BluGeni/Hextraction/STLs/Tiles/King/King Spring.stl

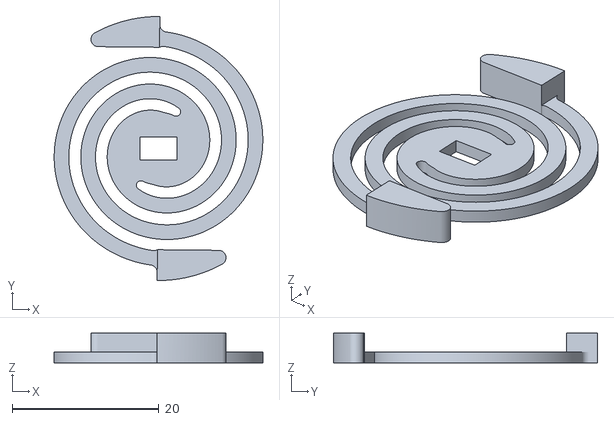
[picture p18: CAD file, 2023-05-18]
STLs/Tiles/King/King Spring.stl
28.5 x 36.0 x 4.05
