BluGeni/Hextraction/STLs/Tiles/Launcher/Launcher Tile Card.stl

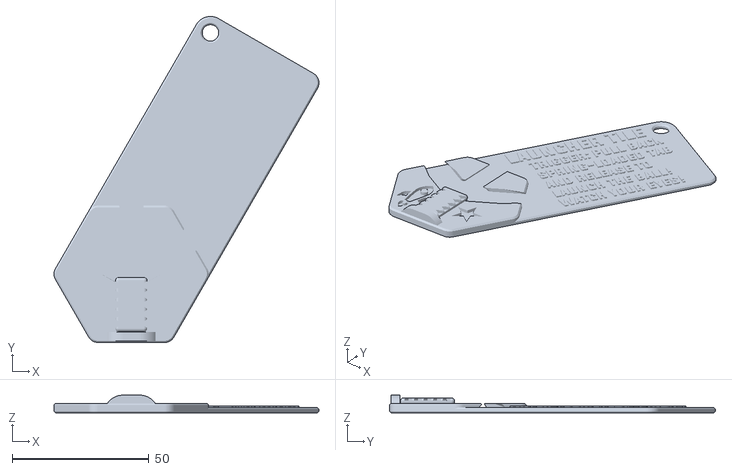
[picture p19: CAD file, 2023-05-18]
STLs/Tiles/Launcher/Launcher Tile Card.stl
96.8 x 119.1 x 6.50
