BluGeni/Hextraction/STLs/Tiles/Logo/Brand Tile 3A.stl

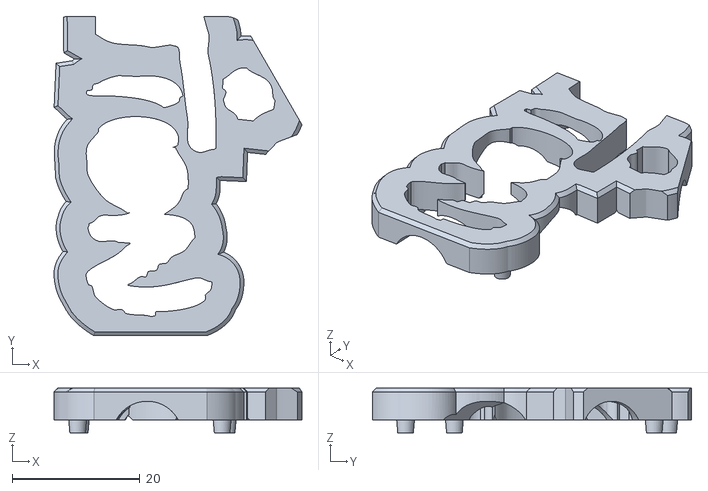
[picture p20: CAD file, 2023-05-18]
STLs/Tiles/Logo/Brand Tile 3A.stl
38.8 x 50.0 x 7.00
