BluGeni/Hextraction/STLs/Tiles/Nothing/Tile with Nothing.stl

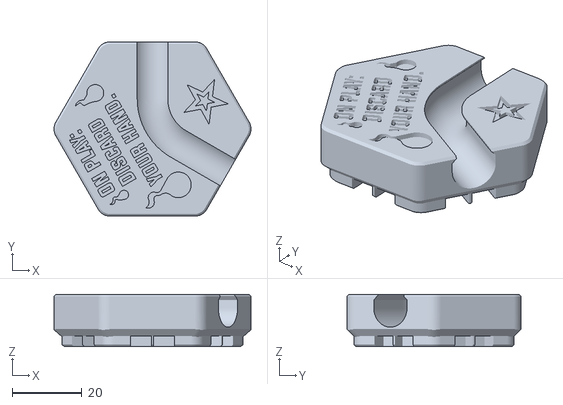
[picture p21: CAD file, 2023-05-18]
STLs/Tiles/Nothing/Tile with Nothing.stl
56.5 x 50.0 x 15.0
