BluGeni/Hextraction/STLs/Tiles/Pachinko/Pachinko Tile.stl

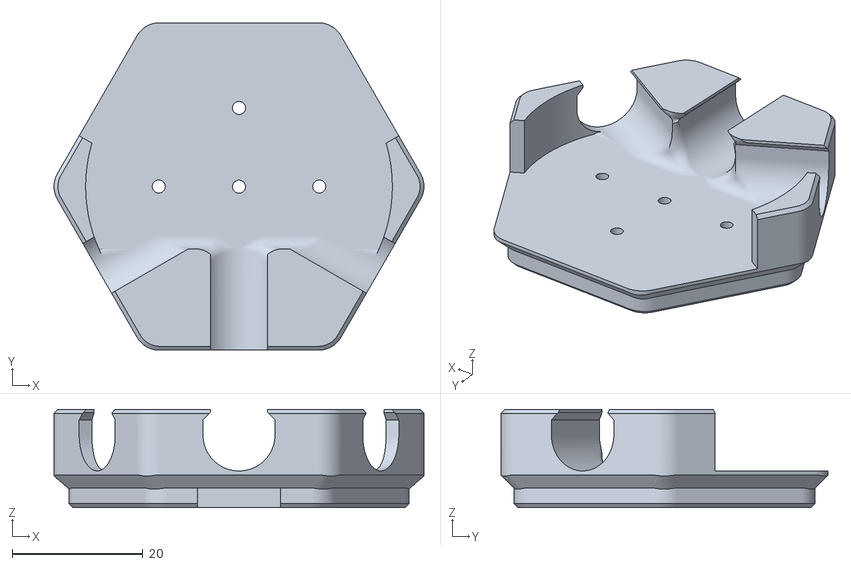
[picture p22: CAD file, 2023-05-18]
STLs/Tiles/Pachinko/Pachinko Tile.stl
56.5 x 50.0 x 15.0
