BluGeni/Hextraction/STLs/Tiles/SecretMystery/Secret Lid.stl

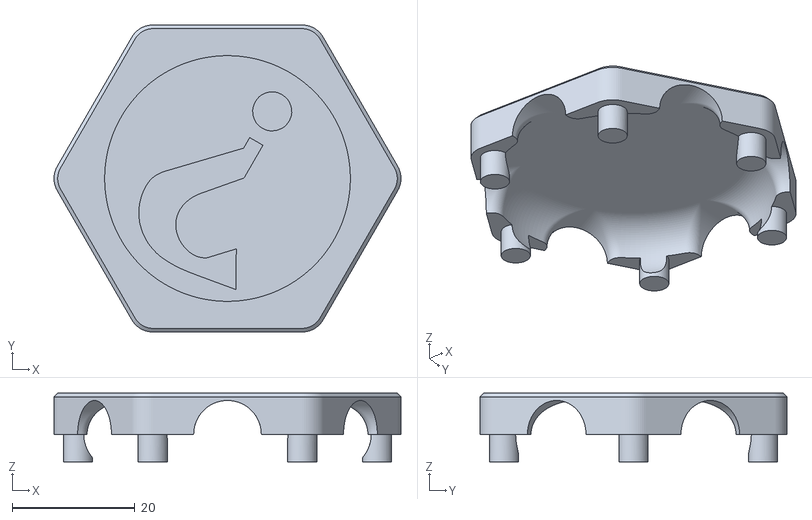
[picture p23: CAD file, 2023-05-18]
STLs/Tiles/SecretMystery/Secret Lid.stl
56.5 x 50.0 x 11.2
