BluGeni/Hextraction/STLs/Tiles/Seek/Seek Tile Multi Center.stl

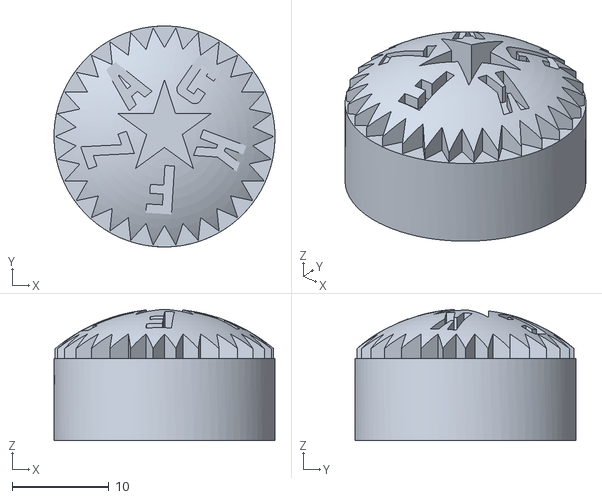
[picture p24: CAD file, 2023-05-18]
STLs/Tiles/Seek/Seek Tile Multi Center.stl
22.8 x 22.8 x 13.6
