BluGeni/Hextraction/STLs/Tiles/Sozu/Sozu Tile v27.stl

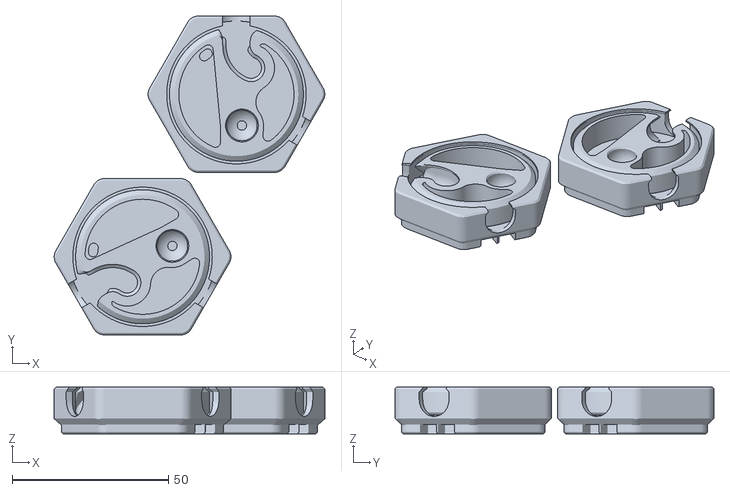
[picture p25: CAD file, 2023-05-18]
STLs/Tiles/Sozu/Sozu Tile v27.stl
86.5 x 102.0 x 15.0
