BluGeni/Hextraction/STLs/Tiles/Teleport/Teleport In Tile.stl

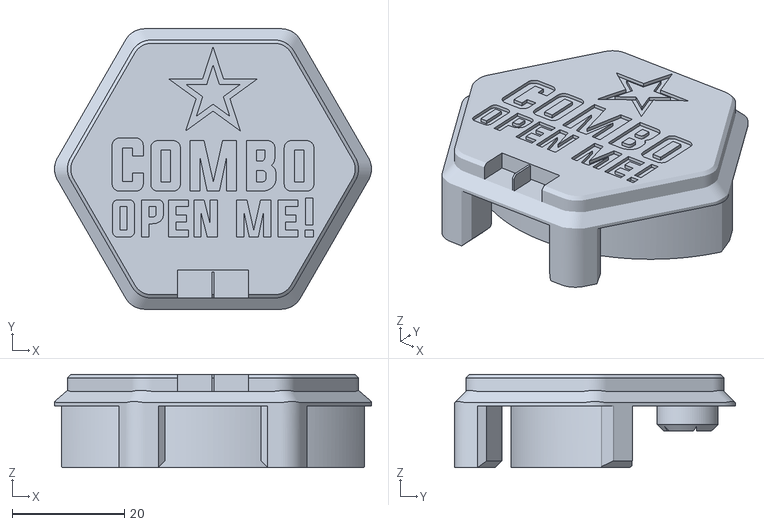
[picture p26: CAD file, 2023-05-18]
STLs/Tiles/Teleport/Teleport In Tile.stl
56.5 x 50.0 x 16.6
