BluGeni/Hextraction/STLs/Tiles/Zoidberg/Zoidberg Tile.stl

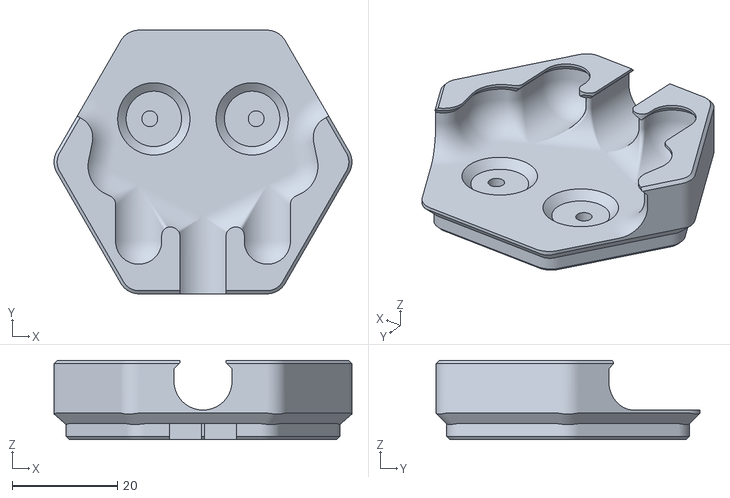
[picture p27: CAD file, 2023-05-18]
STLs/Tiles/Zoidberg/Zoidberg Tile.stl
56.5 x 50.0 x 15.0
