BluGeni/Hextraction/STLs/Tiles/aTemplate/Blank Tile.stl

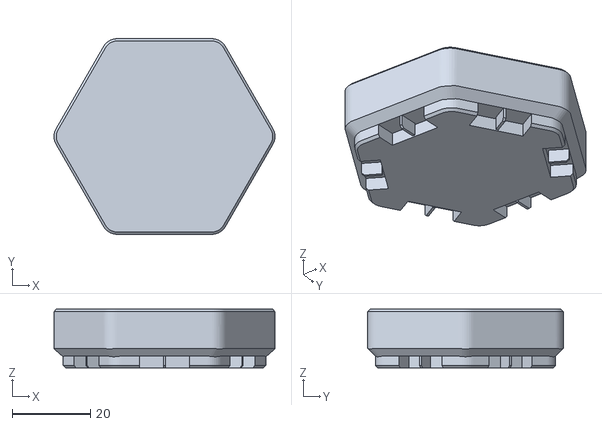
[picture p28: CAD file, 2023-05-18]
STLs/Tiles/aTemplate/Blank Tile.stl
56.5 x 50.0 x 15.0
