BluGeni/Hextraction/STLs/Tiles/Basic/DC Tile.stl

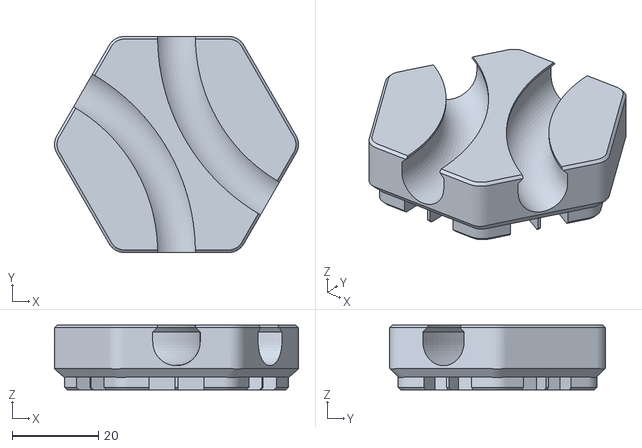
[picture p29: CAD file, 2023-05-18]
STLs/Tiles/Basic/DC Tile.stl
56.5 x 50.0 x 15.0
