BluGeni/Hextraction/STLs/Tiles/Built for Two/Double Tile Link.stl

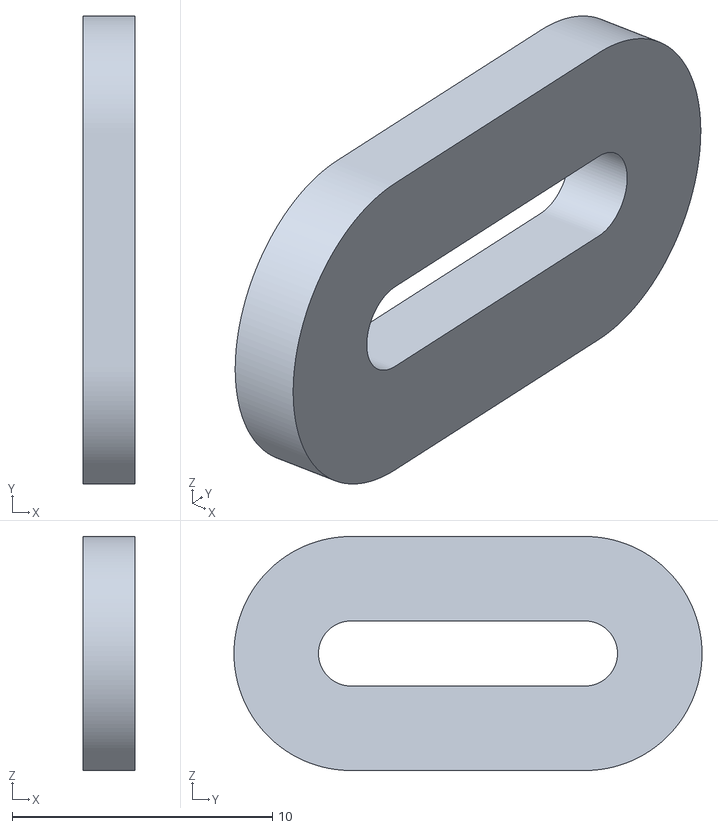
[picture p30: CAD file, 2023-05-18]
STLs/Tiles/Built for Two/Double Tile Link.stl
2.00 x 18.0 x 9.00
