BluGeni/Hextraction/STLs/Tiles/Cartoon Bomb/Bomb Tile Card.stl

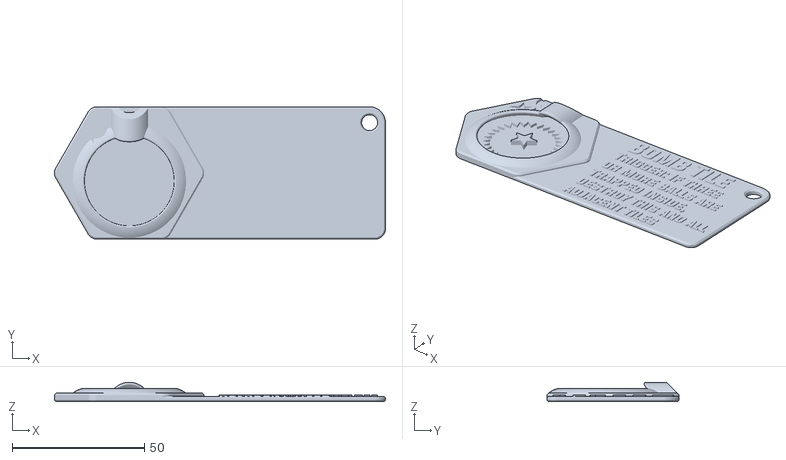
[picture p31: CAD file, 2023-05-18]
STLs/Tiles/Cartoon Bomb/Bomb Tile Card.stl
125.0 x 50.0 x 7.30
