BluGeni/Hextraction/STLs/Tiles/Double and Triple Trap/Triple Trap Tile.stl

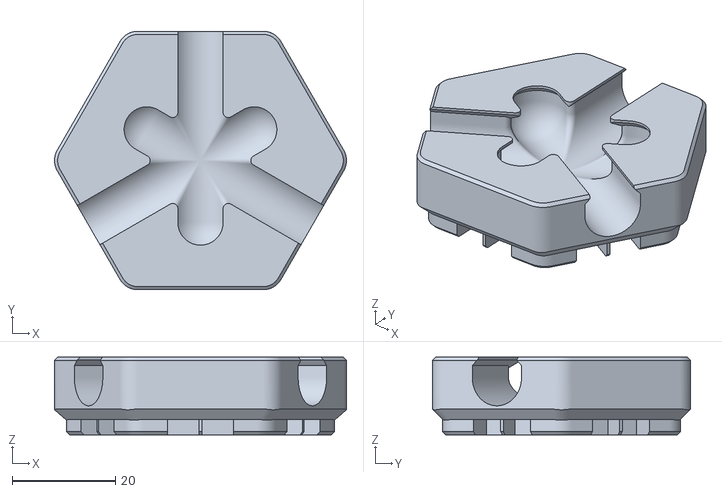
[picture p32: CAD file, 2023-05-18]
STLs/Tiles/Double and Triple Trap/Triple Trap Tile.stl
56.5 x 50.0 x 15.0
