BluGeni/Hextraction/STLs/Tiles/Flip-Flop/Flip Tile.step

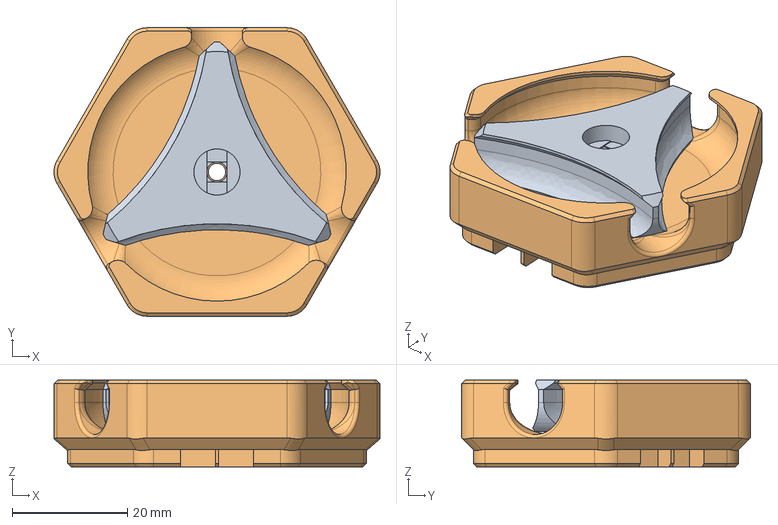
[picture p33: CAD file, 2023-05-18]
STLs/Tiles/Flip-Flop/Flip Tile.step
56.5 x 50.0 x 15.0 mm
Flippy Dingus
Tile (1)
