BluGeni/Hextraction/STLs/Tiles/Holographic/Holographic Hypertile v16.step

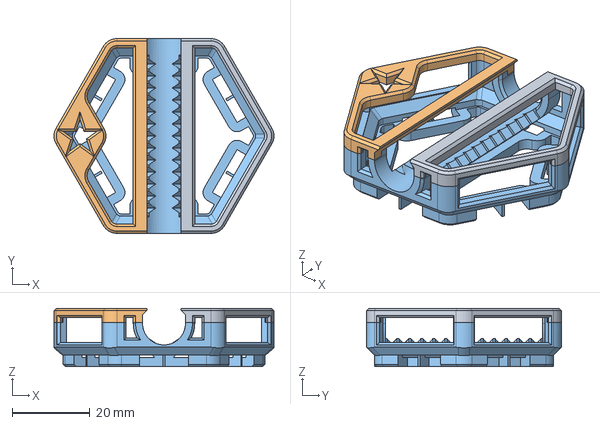
[picture p34: CAD file, 2023-05-18]
STLs/Tiles/Holographic/Holographic Hypertile v16.step
56.5 x 50.0 x 15.0 mm
