BluGeni/Hextraction/STLs/Tiles/King/King Upper.stl

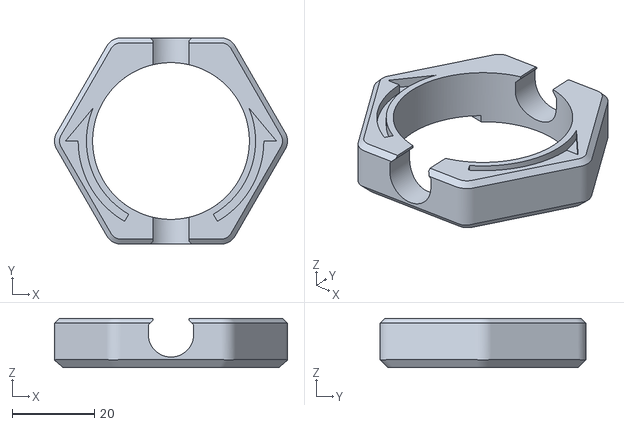
[picture p35: CAD file, 2023-05-18]
STLs/Tiles/King/King Upper.stl
56.5 x 50.0 x 12.0
