BluGeni/Hextraction/STLs/Tiles/Launcher/Launcher Tile.stl

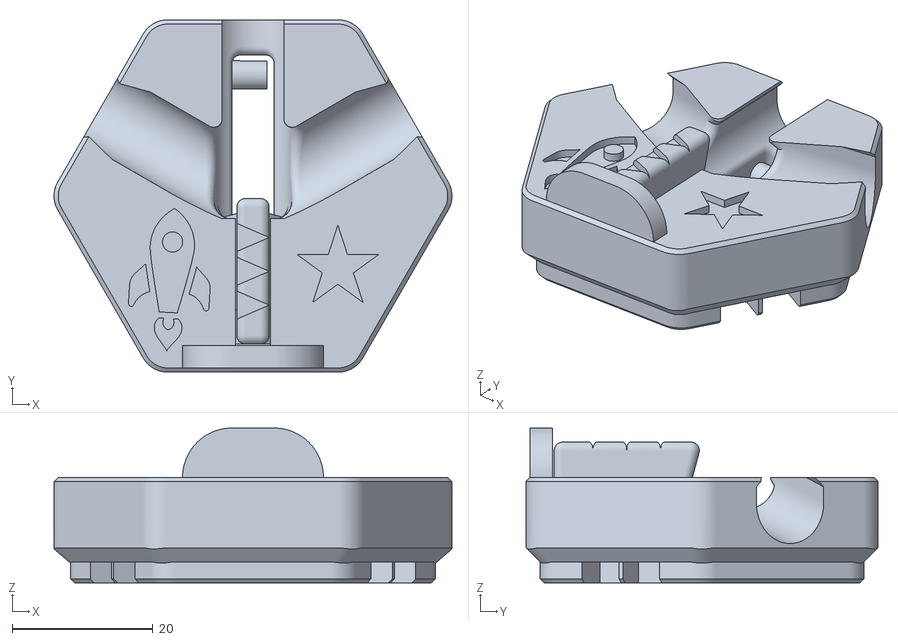
[picture p36: CAD file, 2023-05-18]
STLs/Tiles/Launcher/Launcher Tile.stl
56.5 x 50.0 x 22.0
