BluGeni/Hextraction/STLs/Tiles/Logo/Brand Tile 3B.stl

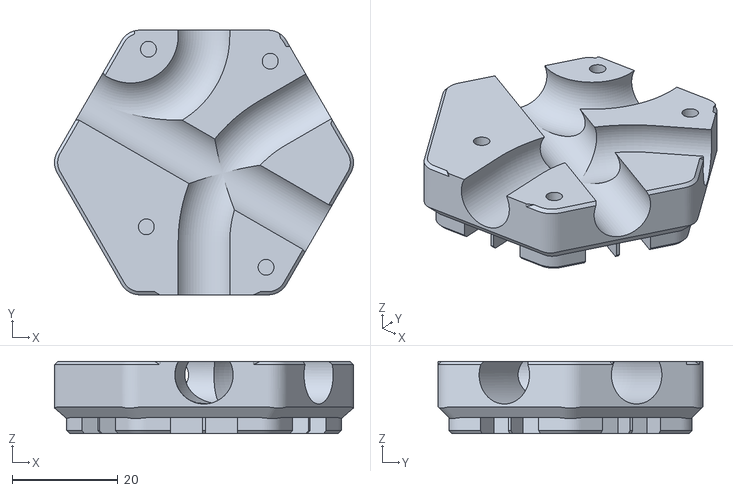
[picture p37: CAD file, 2023-05-18]
STLs/Tiles/Logo/Brand Tile 3B.stl
56.5 x 50.0 x 13.7
