BluGeni/Hextraction/STLs/Tiles/SecretMystery/Secret DC Body.stl

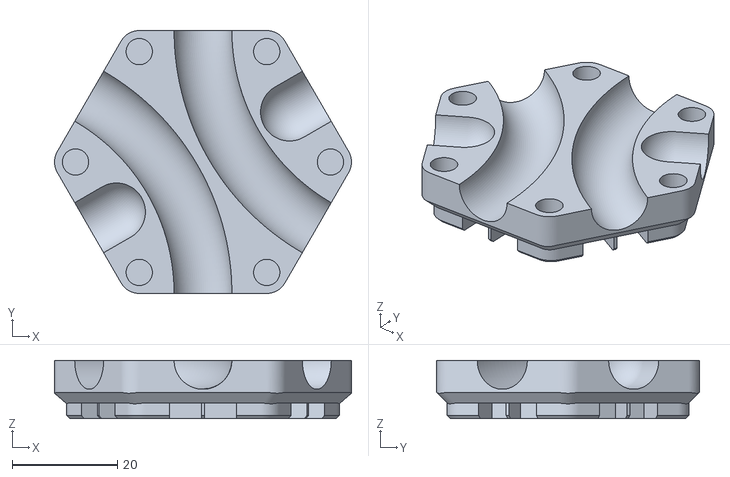
[picture p38: CAD file, 2023-05-18]
STLs/Tiles/SecretMystery/Secret DC Body.stl
56.5 x 50.0 x 11.1
