BluGeni/Hextraction/STLs/Tiles/Seek/Seek Tile Card.stl

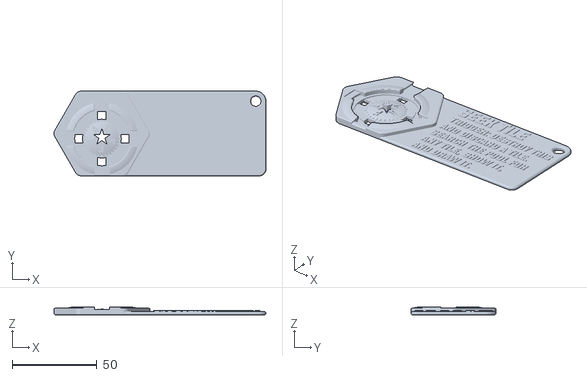
[picture p39: CAD file, 2023-05-18]
STLs/Tiles/Seek/Seek Tile Card.stl
125.0 x 50.0 x 4.73
