BluGeni/Hextraction/STLs/Game Board/Basic On-Ramp.stl

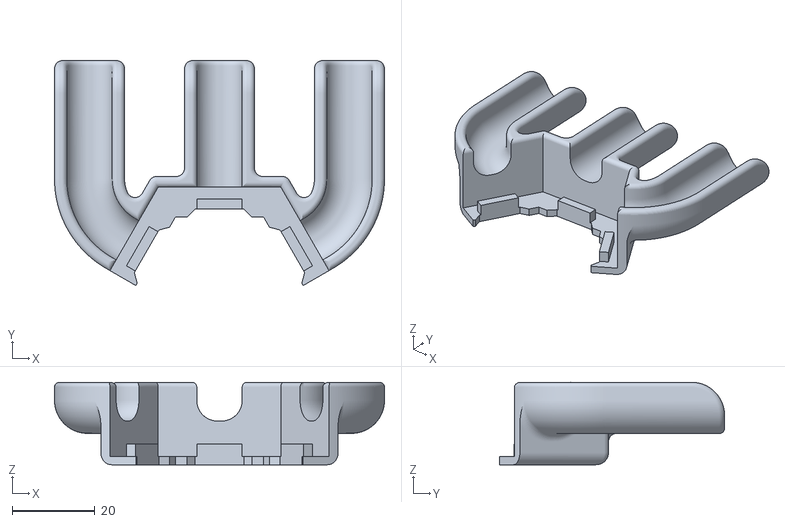
[picture p41: CAD file, 2023-05-18]
STLs/Game Board/Basic On-Ramp.stl
80.0 x 54.6 x 20.0
