BluGeni/Hextraction/STLs/Tiles/Basic/Peace Tile.stl

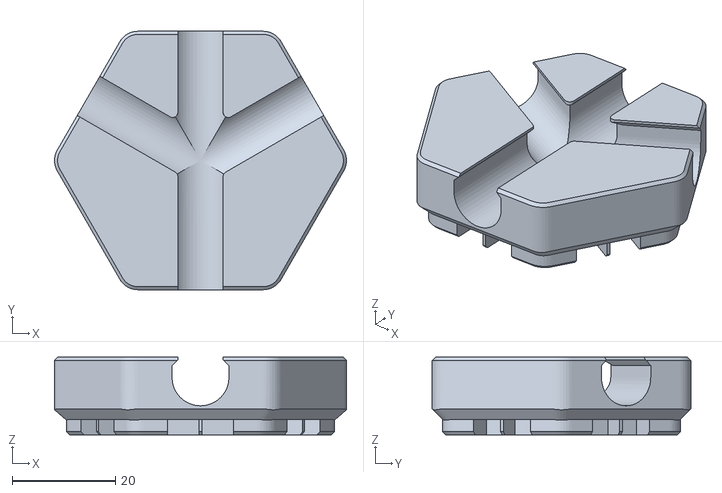
[picture p42: CAD file, 2023-05-18]
STLs/Tiles/Basic/Peace Tile.stl
56.5 x 50.0 x 15.0
