BluGeni/Hextraction/STLs/Tiles/Built for Two/Double Tile Top.stl

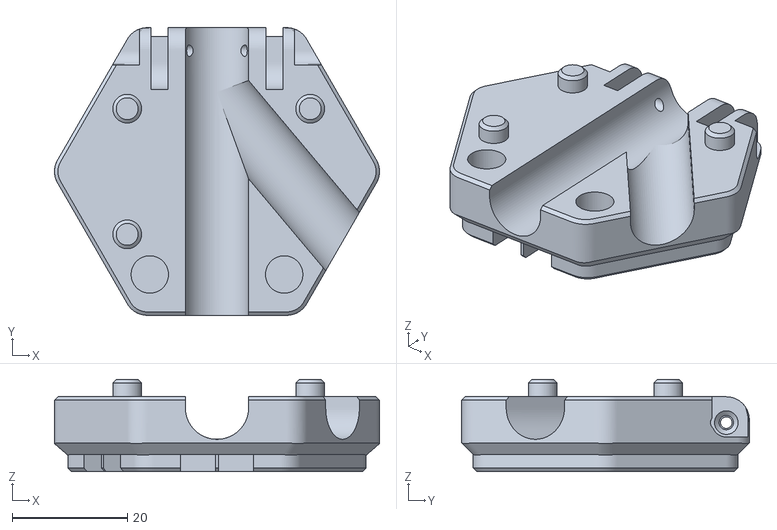
[picture p43: CAD file, 2023-05-18]
STLs/Tiles/Built for Two/Double Tile Top.stl
56.5 x 50.0 x 16.0
