BluGeni/Hextraction/STLs/Tiles/Flip-Flop/Flip Flop Tile Advanced.stl

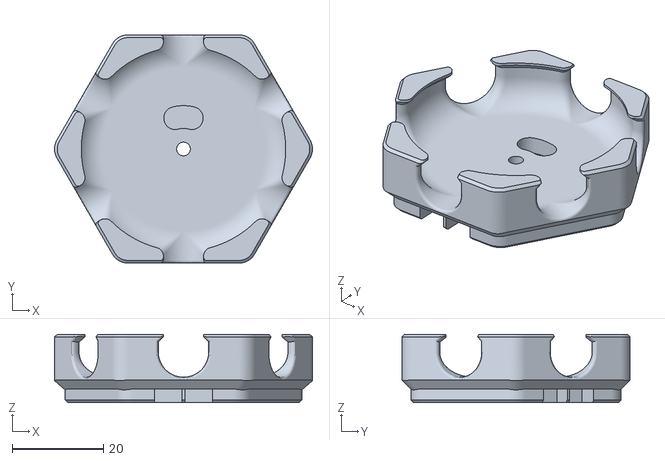
[picture p44: CAD file, 2023-05-18]
STLs/Tiles/Flip-Flop/Flip Flop Tile Advanced.stl
56.5 x 50.0 x 15.0
