BluGeni/Hextraction/STLs/Tiles/Holographic/Holo Bottom.stl

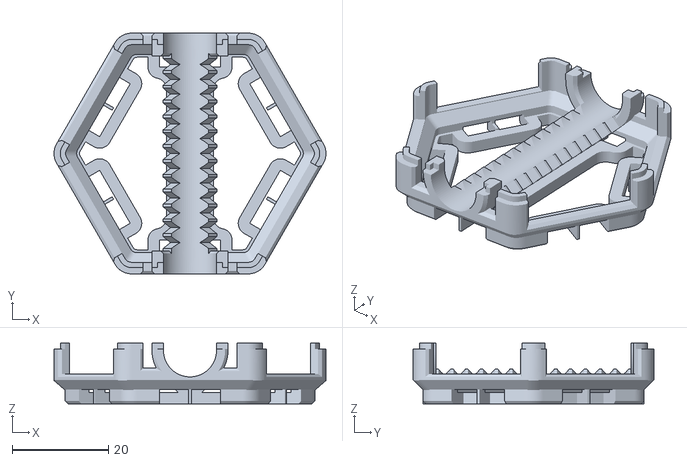
[picture p45: CAD file, 2023-05-18]
STLs/Tiles/Holographic/Holo Bottom.stl
56.5 x 50.0 x 12.6
