BluGeni/Hextraction/STLs/Tiles/King/King Lower.stl

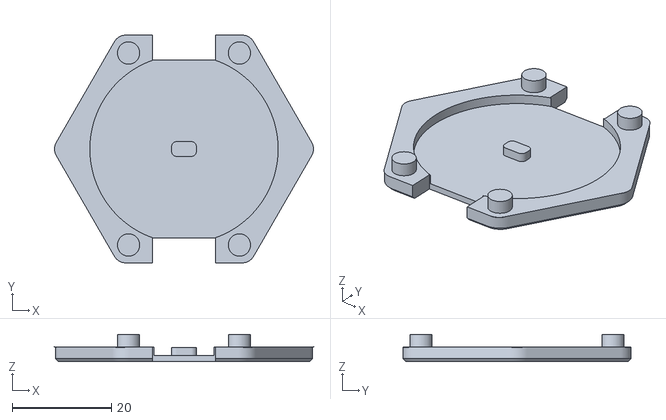
[picture p46: CAD file, 2023-05-18]
STLs/Tiles/King/King Lower.stl
52.3 x 46.0 x 5.50
