BluGeni/Hextraction/STLs/Tiles/Logo/Brand Tile 1A.stl

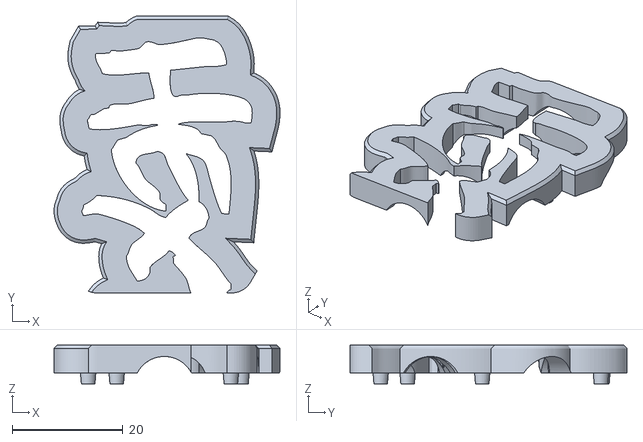
[picture p47: CAD file, 2023-05-18]
STLs/Tiles/Logo/Brand Tile 1A.stl
40.8 x 50.0 x 7.00
