BluGeni/Hextraction/STLs/Tiles/SecretMystery/Secret Inlay.stl

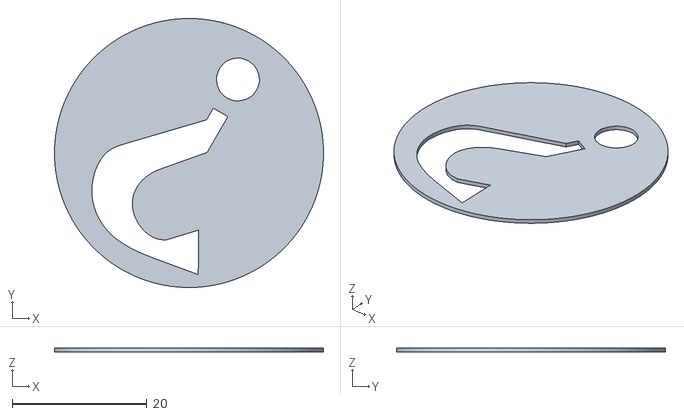
[picture p48: CAD file, 2023-05-18]
STLs/Tiles/SecretMystery/Secret Inlay.stl
40.0 x 40.0 x 0.6
