BluGeni/Hextraction/STLs/Tiles/Seek/Seek Tile One Piece.stl

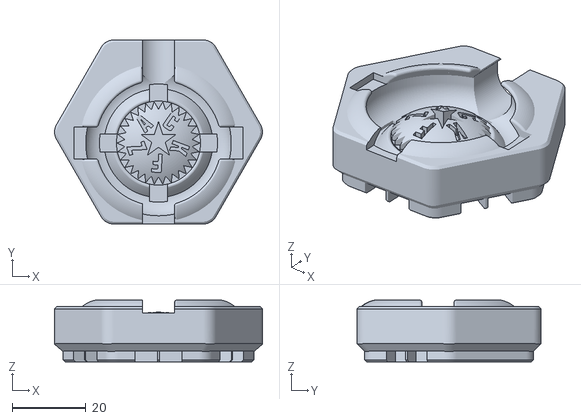
[picture p49: CAD file, 2023-05-18]
STLs/Tiles/Seek/Seek Tile One Piece.stl
56.5 x 50.0 x 16.8
