BluGeni/Hextraction/STLs/Tiles/Sozu/Sozu Flipper Right 3-8in.stl

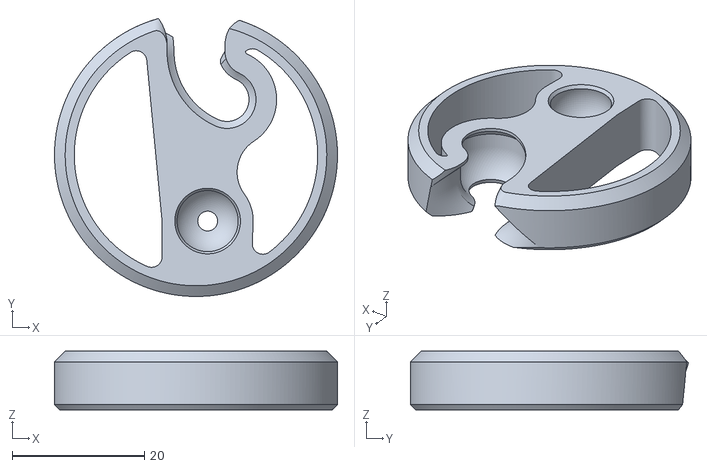
[picture p50: CAD file, 2023-05-18]
STLs/Tiles/Sozu/Sozu Flipper Right 3-8in.stl
42.8 x 42.0 x 8.90
