BluGeni/Hextraction/STLs/Tiles/Built for Two/Tile Built for Two v11.step

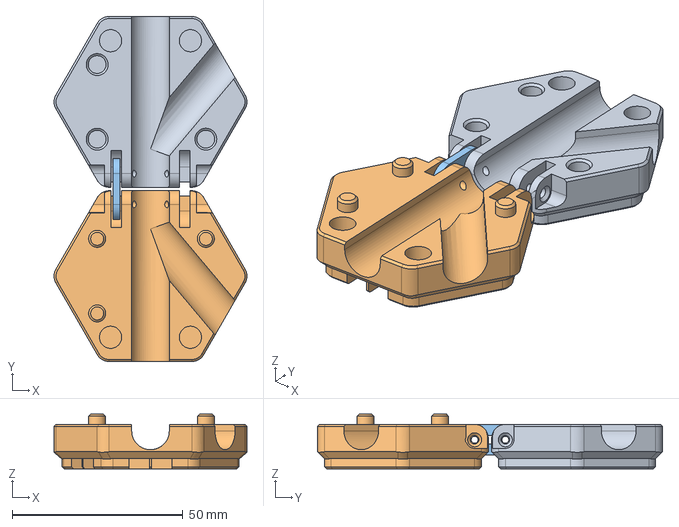
[picture p52: CAD file, 2023-05-18]
STLs/Tiles/Built for Two/Tile Built for Two v11.step
56.5 x 101.0 x 16.0 mm
