BluGeni/Hextraction/STLs/Tiles/Holographic/Holo Card.stl

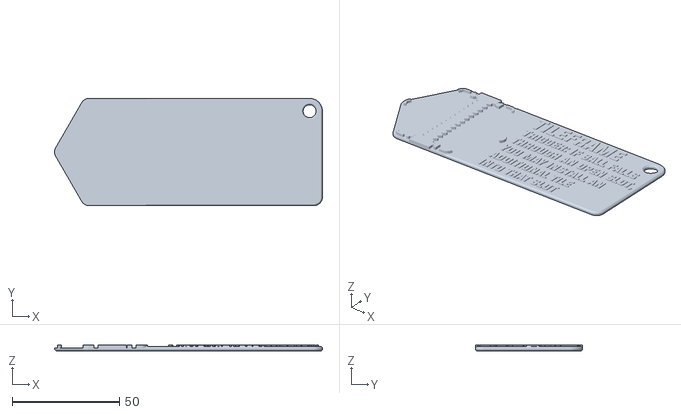
[picture p53: CAD file, 2023-05-18]
STLs/Tiles/Holographic/Holo Card.stl
125.0 x 50.0 x 2.60
