BluGeni/Hextraction/STLs/Tiles/King/King Tile v19.step

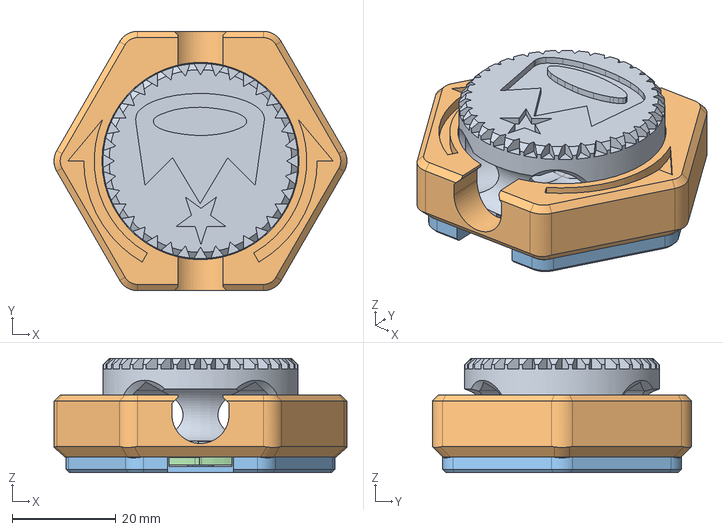
[picture p54: CAD file, 2023-05-18]
STLs/Tiles/King/King Tile v19.step
56.5 x 50.0 x 22.0 mm
