BluGeni/Hextraction/STLs/Tiles/Seek/Seek Tile Multi.stl

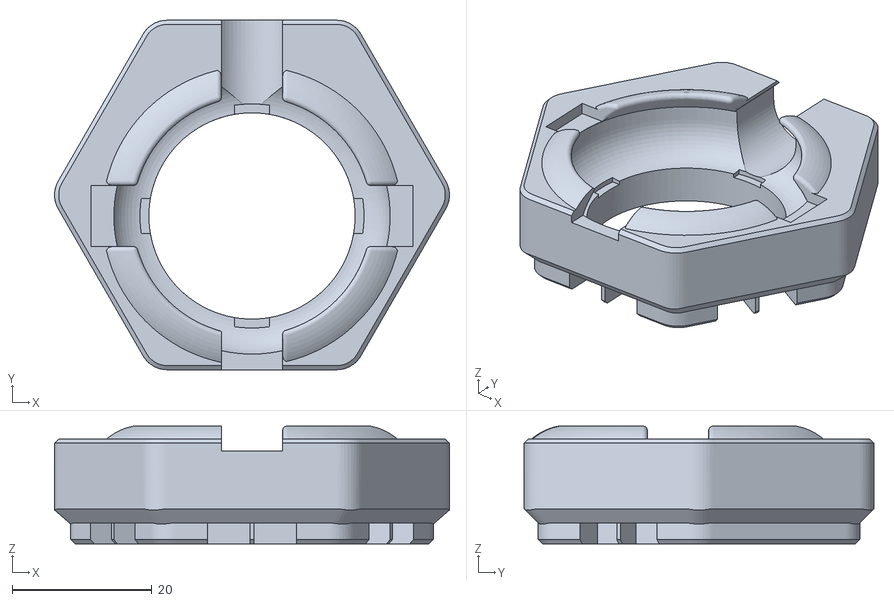
[picture p55: CAD file, 2023-05-18]
STLs/Tiles/Seek/Seek Tile Multi.stl
56.5 x 50.0 x 16.8
