BluGeni/Hextraction/STLs/Tiles/Teleport/Teleport Out Tile.stl

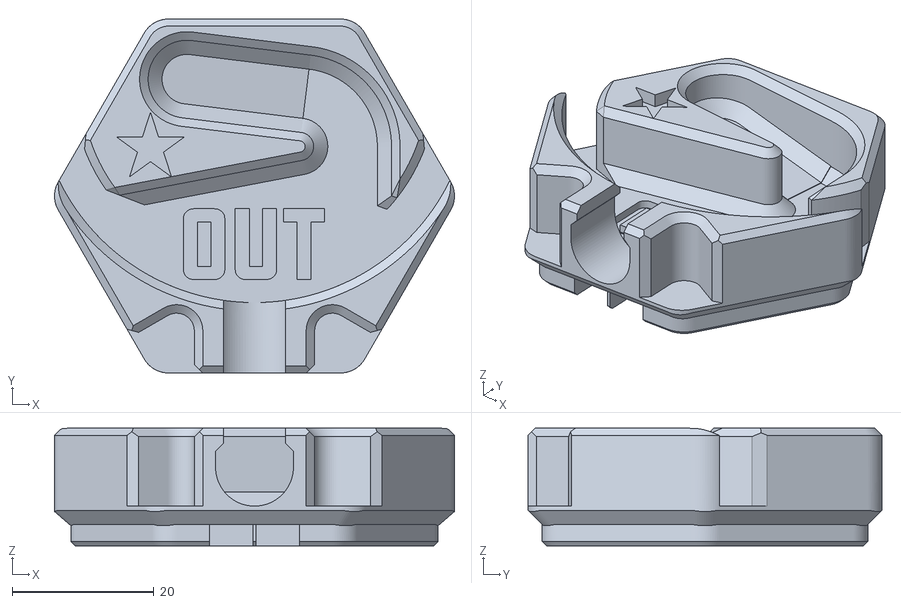
[picture p56: CAD file, 2023-05-18]
STLs/Tiles/Teleport/Teleport Out Tile.stl
56.5 x 50.0 x 16.6
