BluGeni/Hextraction/STLs/Game Board/Universal End Zone.stl

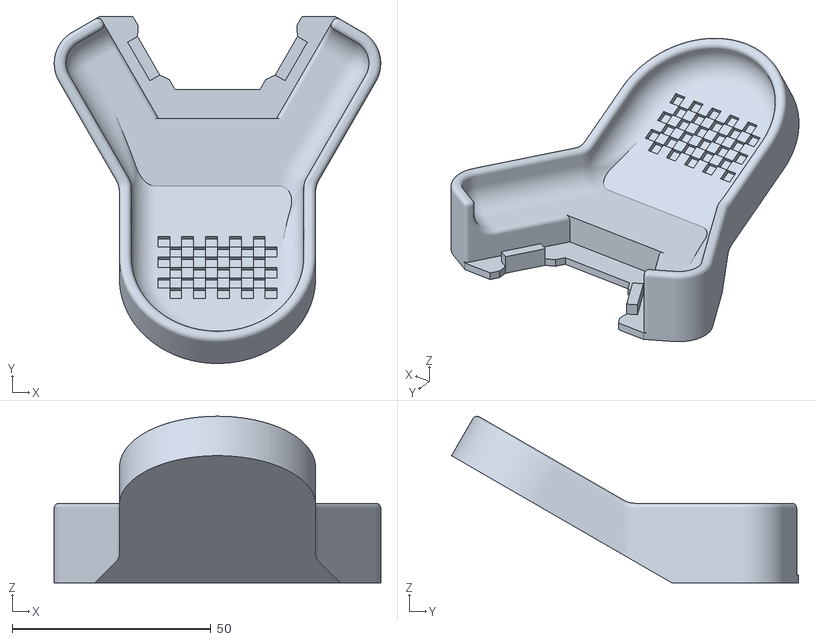
[picture p57: CAD file, 2023-05-18]
STLs/Game Board/Universal End Zone.stl
82.2 x 87.3 x 41.9
