BluGeni/Hextraction/STLs/Tiles/Holographic/Holo Right Top.stl

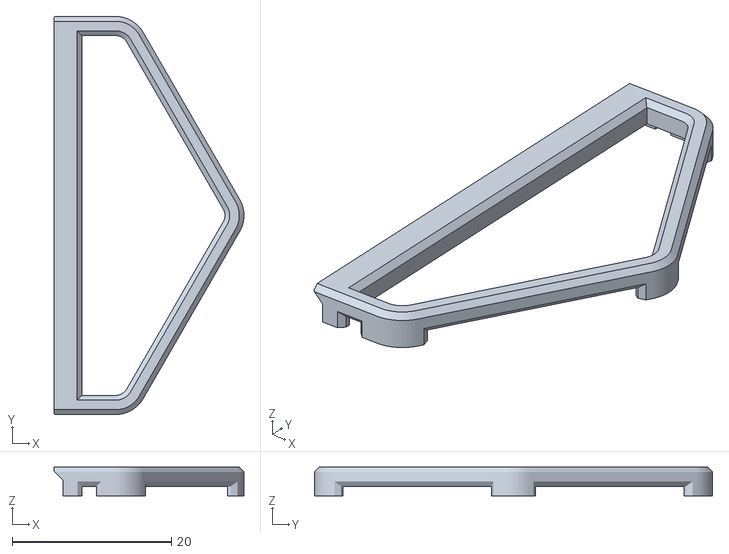
[picture p58: CAD file, 2023-05-18]
STLs/Tiles/Holographic/Holo Right Top.stl
23.9 x 50.0 x 3.60
