BluGeni/Hextraction/STLs/Tiles/King/King Knob.stl

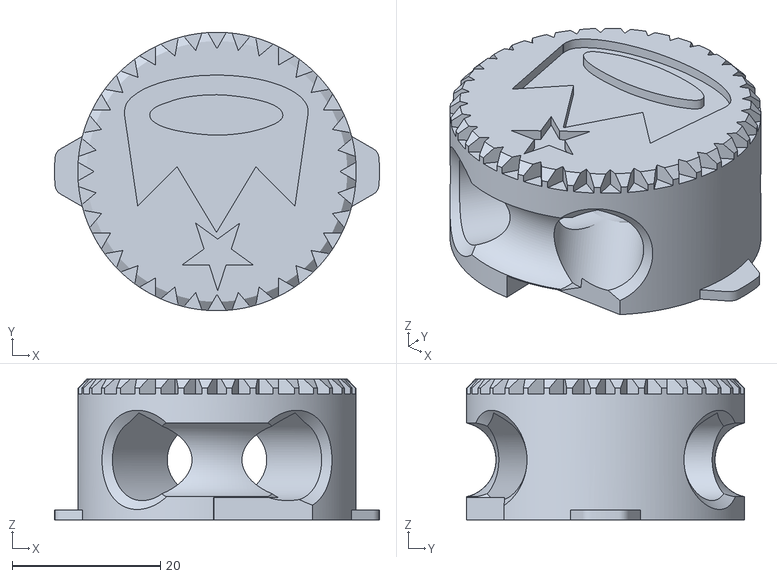
[picture p59: CAD file, 2023-05-18]
STLs/Tiles/King/King Knob.stl
43.9 x 37.6 x 19.0
