BluGeni/Hextraction/STLs/Tiles/Logo/Brand Overlay 1.stl

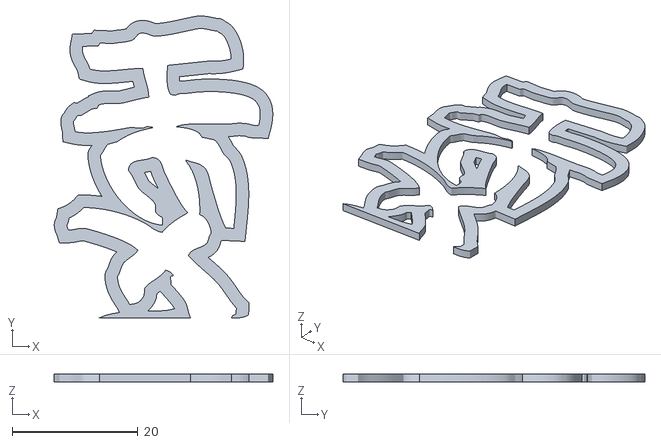
[picture p60: CAD file, 2023-05-18]
STLs/Tiles/Logo/Brand Overlay 1.stl
34.8 x 48.1 x 1.20
