BluGeni/Hextraction/STLs/Tiles/SecretMystery/Secret Lil DC.stl

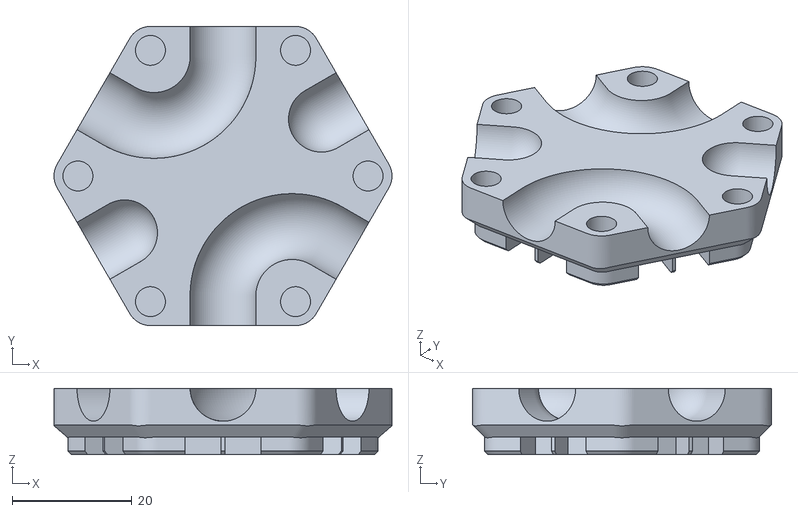
[picture p61: CAD file, 2023-05-18]
STLs/Tiles/SecretMystery/Secret Lil DC.stl
56.5 x 50.0 x 11.1
