BluGeni/Hextraction/STLs/Tiles/Seek/Seek Tile Multi Ring.stl

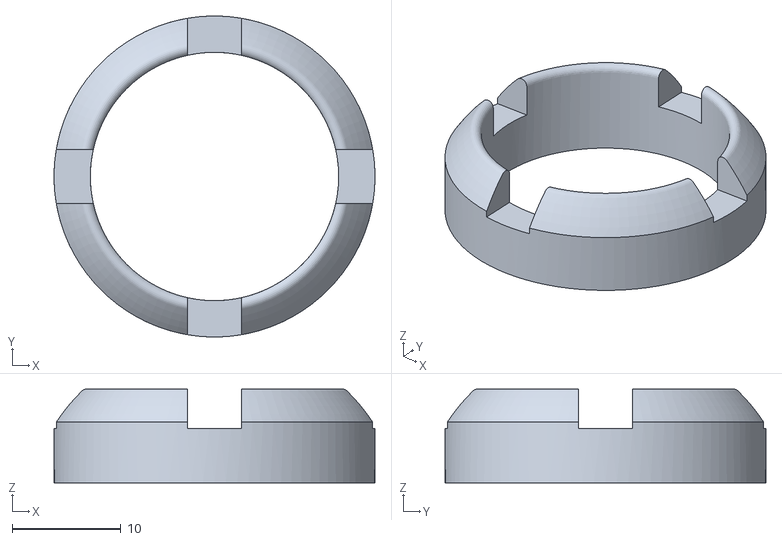
[picture p62: CAD file, 2023-05-18]
STLs/Tiles/Seek/Seek Tile Multi Ring.stl
29.5 x 29.5 x 8.63
