BluGeni/Hextraction/STLs/Game Board/Gutter Foot Mount Integrated.stl

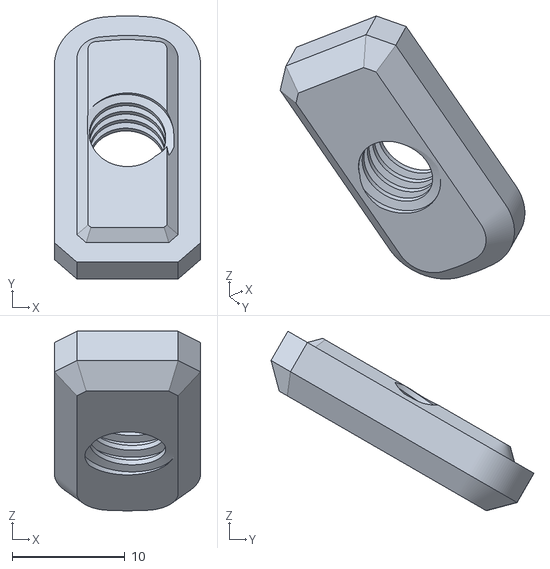
[picture p63: CAD file, 2023-05-18]
STLs/Game Board/Gutter Foot Mount Integrated.stl
13.0 x 23.4 x 16.0
