BluGeni/Hextraction/STLs/Tiles/Logo/Brand Overlay 3.stl

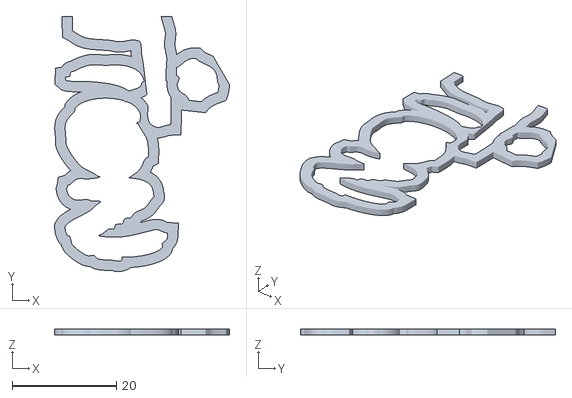
[picture p64: CAD file, 2023-05-18]
STLs/Tiles/Logo/Brand Overlay 3.stl
33.6 x 49.0 x 1.20
