BluGeni/Hextraction/STLs/Game Board/Gutter Segment.stl

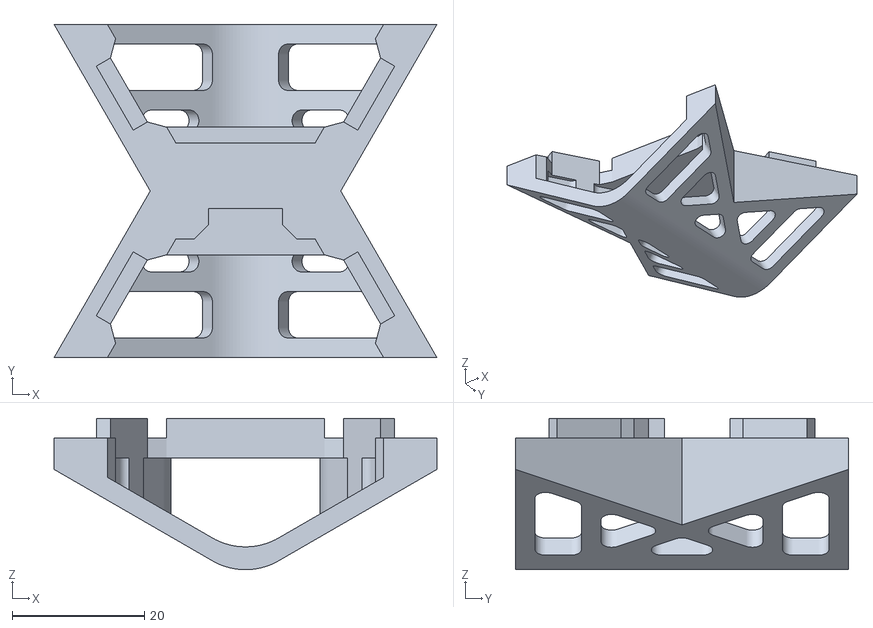
[picture p65: CAD file, 2023-05-18]
STLs/Game Board/Gutter Segment.stl
58.0 x 50.5 x 22.9
