BluGeni/Hextraction/STLs/Tiles/Logo/Brand Tile 2B.stl

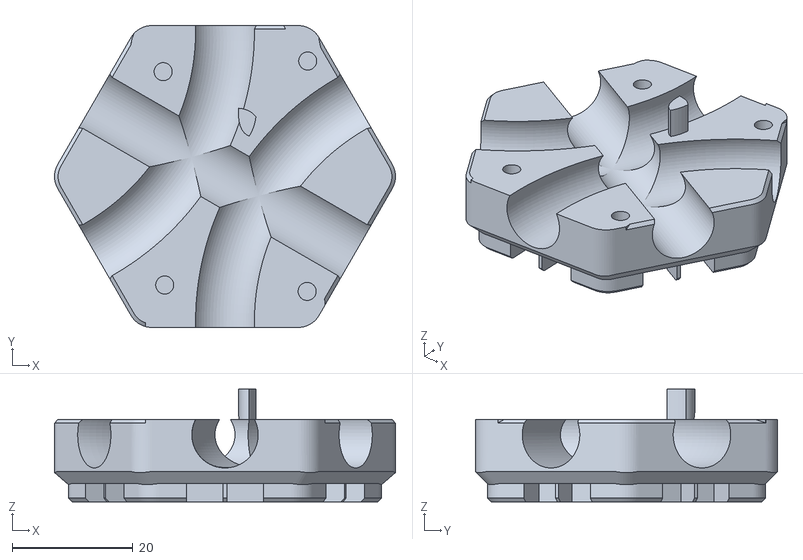
[picture p66: CAD file, 2023-05-18]
STLs/Tiles/Logo/Brand Tile 2B.stl
56.5 x 50.0 x 18.7
