BluGeni/Hextraction/STLs/Tiles/SecretMystery/Secret Flippy Body.stl

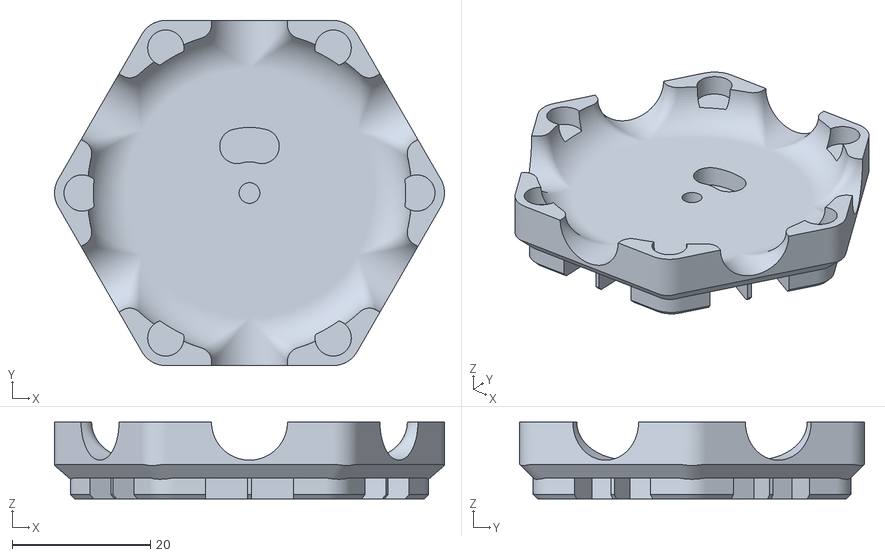
[picture p67: CAD file, 2023-05-18]
STLs/Tiles/SecretMystery/Secret Flippy Body.stl
56.5 x 50.0 x 11.1
