BluGeni/Hextraction/STLs/Tiles/Logo/Brand Overlay 2.stl

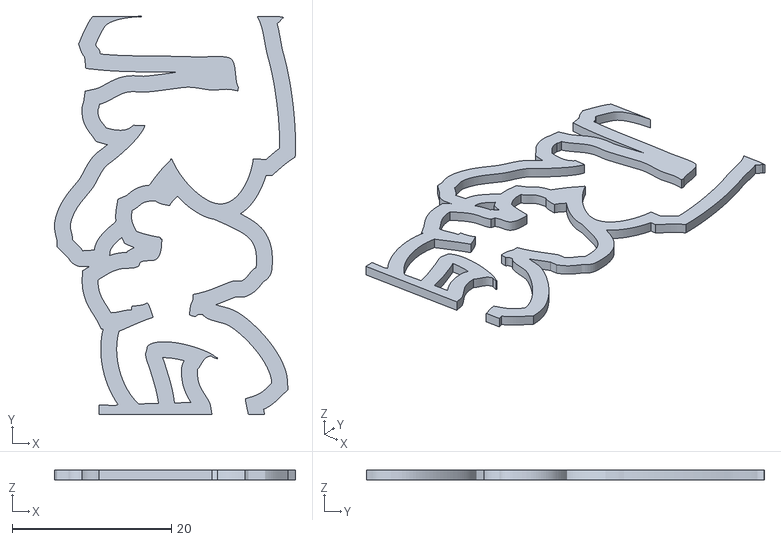
[picture p68: CAD file, 2023-05-18]
STLs/Tiles/Logo/Brand Overlay 2.stl
30.3 x 50.0 x 1.20
