BluGeni/Hextraction/STLs/Game Board/Basic Foot Mount Heat Set.stl

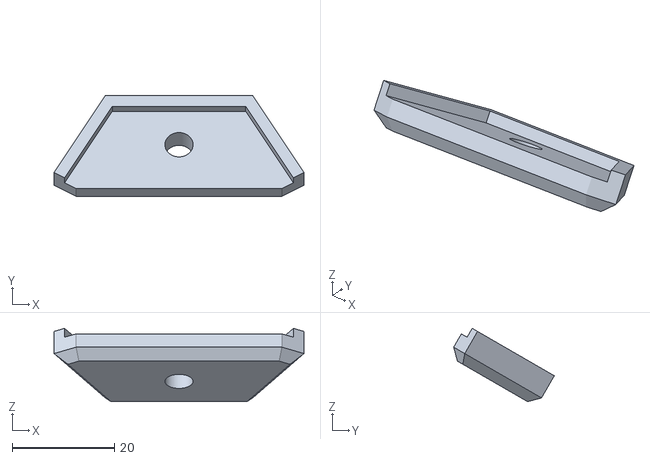
[picture p69: CAD file, 2023-05-18]
STLs/Game Board/Basic Foot Mount Heat Set.stl
48.9 x 19.7 x 14.3
