BluGeni/Hextraction/STLs/Tiles/Logo/Brand Tile 2A.stl

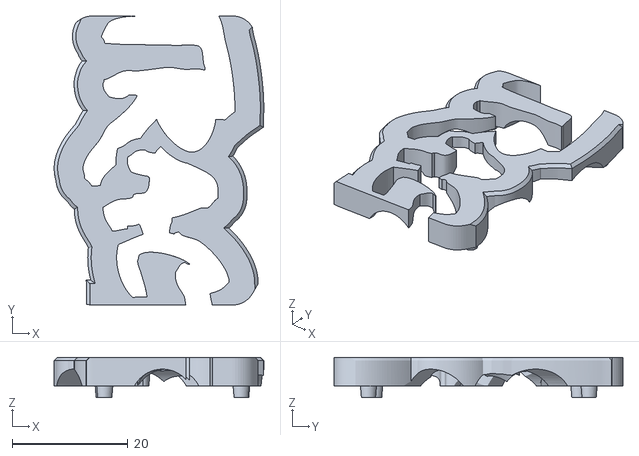
[picture p70: CAD file, 2023-05-18]
STLs/Tiles/Logo/Brand Tile 2A.stl
36.3 x 50.0 x 7.00
