BluGeni/Hextraction/STLs/Game Board/5-7 Plate.stl

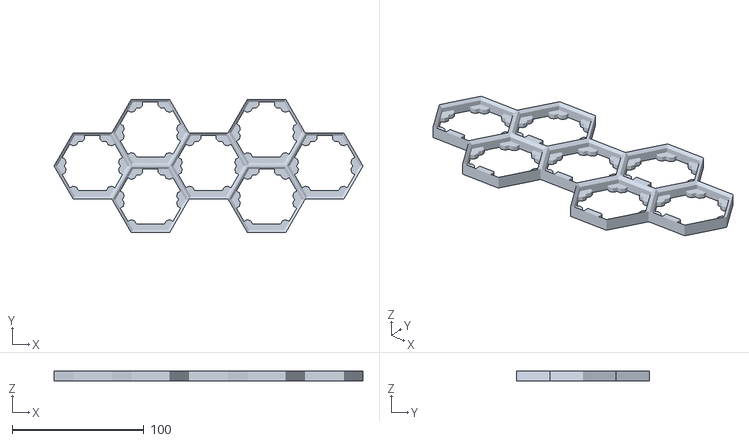
[picture p71: CAD file, 2023-05-18]
STLs/Game Board/5-7 Plate.stl
235.0 x 101.5 x 7.75
