BluGeni/Hextraction/STLs/Tiles/Logo/Brand Overlay R Bit.stl

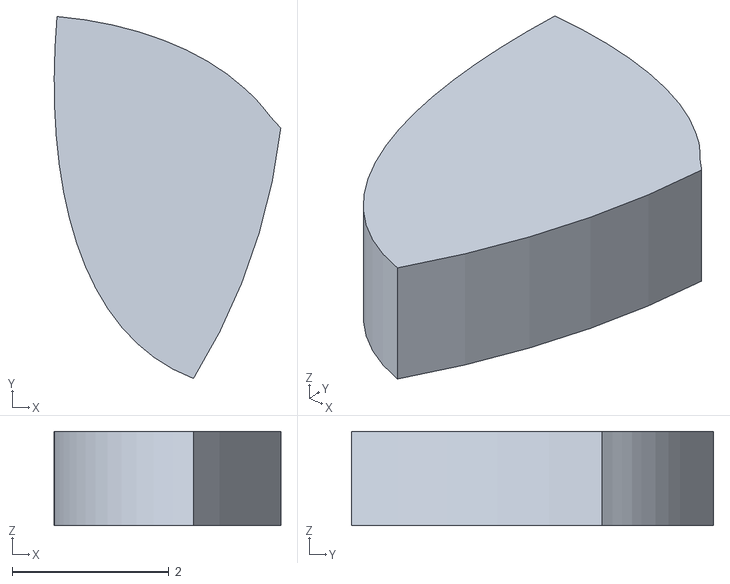
[picture p72: CAD file, 2023-05-18]
STLs/Tiles/Logo/Brand Overlay R Bit.stl
2.89 x 4.62 x 1.20
