BluGeni/Hextraction/STLs/Game Board/Universal Foot M4.stl

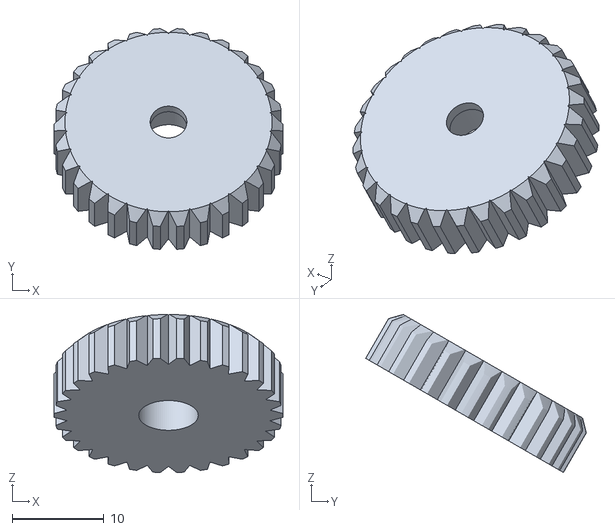
[picture p74: CAD file, 2023-05-18]
STLs/Game Board/Universal Foot M4.stl
25.0 x 24.1 x 17.3
