BluGeni/Hextraction/STLs/Game Board/Basic Leg Segment 12mm.stl

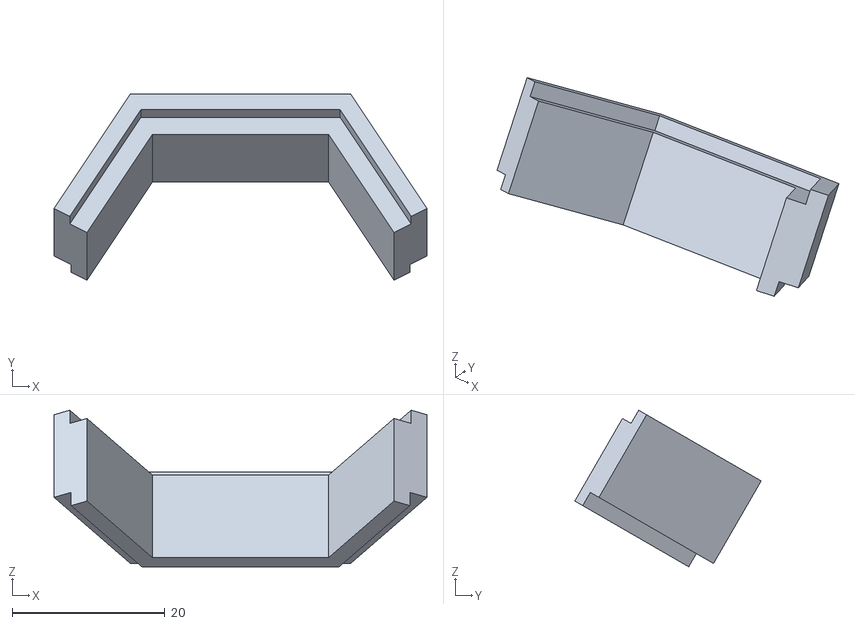
[picture p75: CAD file, 2023-05-18]
STLs/Game Board/Basic Leg Segment 12mm.stl
48.9 x 24.4 x 20.5
