BluGeni/Hextraction/STLs/Game Board/5-15 Plate.stl

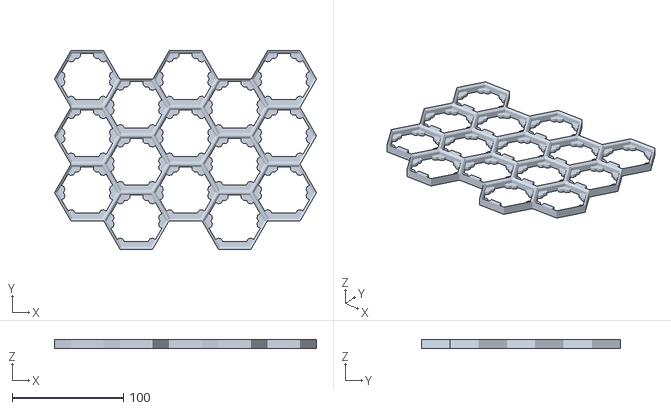
[picture p76: CAD file, 2023-05-18]
STLs/Game Board/5-15 Plate.stl
235.3 x 178.3 x 7.75
