BluGeni/Hextraction/STLs/Game Board/Gutter Leg Segment 50mm.stl

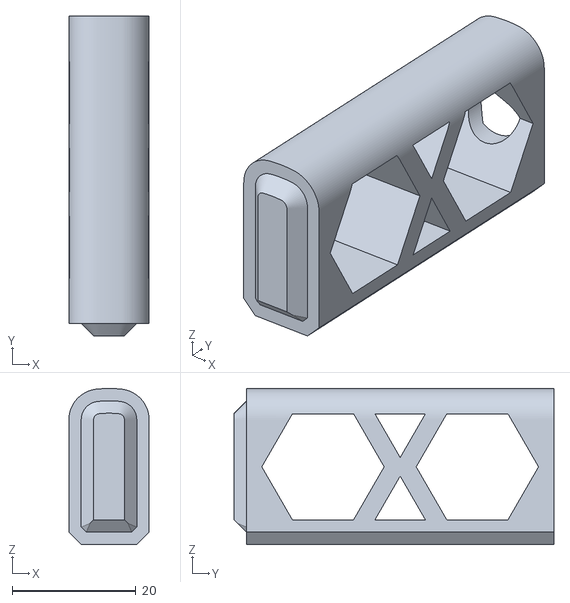
[picture p77: CAD file, 2023-05-18]
STLs/Game Board/Gutter Leg Segment 50mm.stl
13.0 x 51.8 x 25.3
