BluGeni/Hextraction/STLs/Game Board/hexstraction.3mf

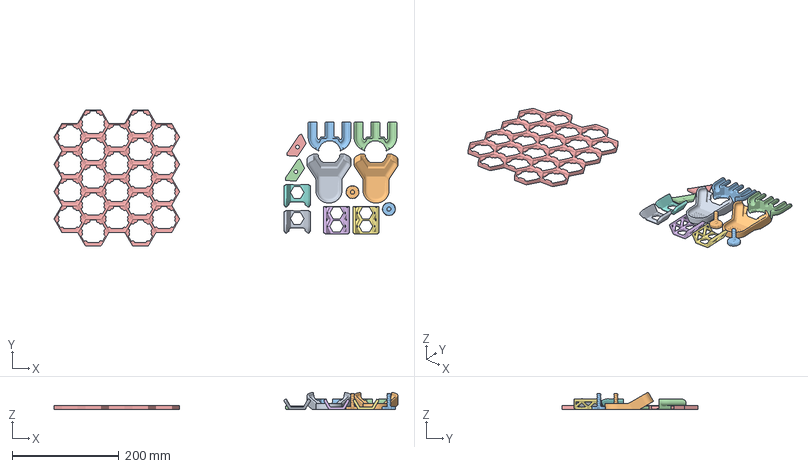
[picture p78: CAD file, 2023-05-18]
STLs/Game Board/hexstraction.3mf
644.3 x 254.8 x 32.6 mm
Universal End Zone.stl
Basic On-Ramp.stl
Baseplate v2.stl
Basic Leg Segment 50mm.stl
Basic Front Leg Mount.stl
Universal Foot Integrated.stl
Basic Foot Mount Integrated.stl
