BluGeni/Hextraction/STLs/Game Board/Gutter On-Ramp.stl

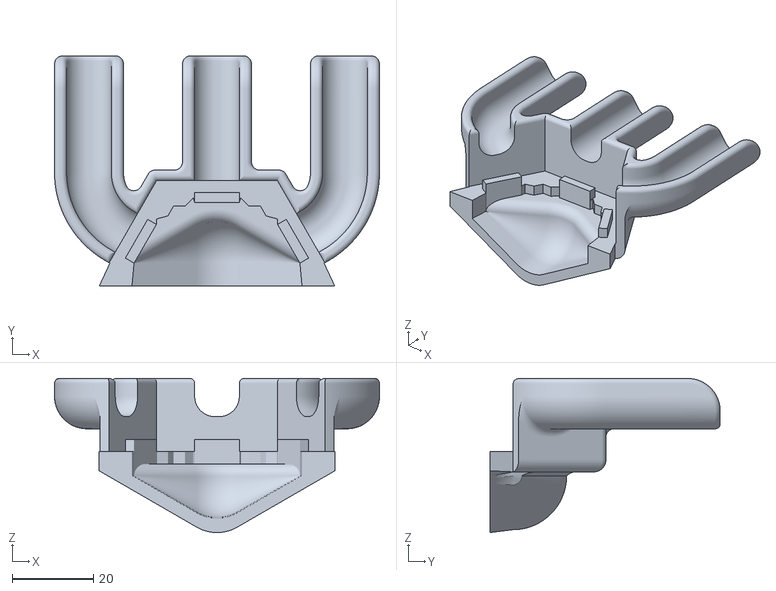
[picture p79: CAD file, 2023-05-18]
STLs/Game Board/Gutter On-Ramp.stl
80.0 x 56.7 x 37.9
