BluGeni/Hextraction/STLs/Game Board/Gutter Leg Mount.stl

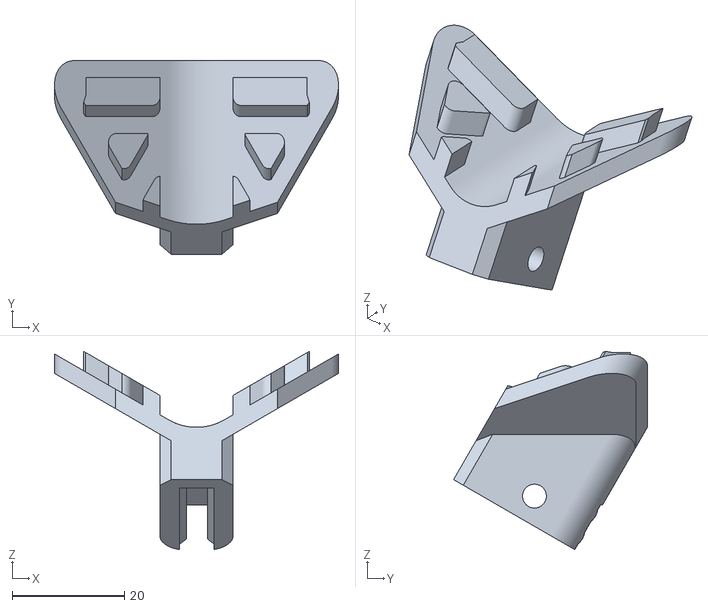
[picture p80: CAD file, 2023-05-18]
STLs/Game Board/Gutter Leg Mount.stl
50.6 x 34.6 x 35.3
