BluGeni/Hextraction/STLs/Game Board/Universal Foot Integrated.stl

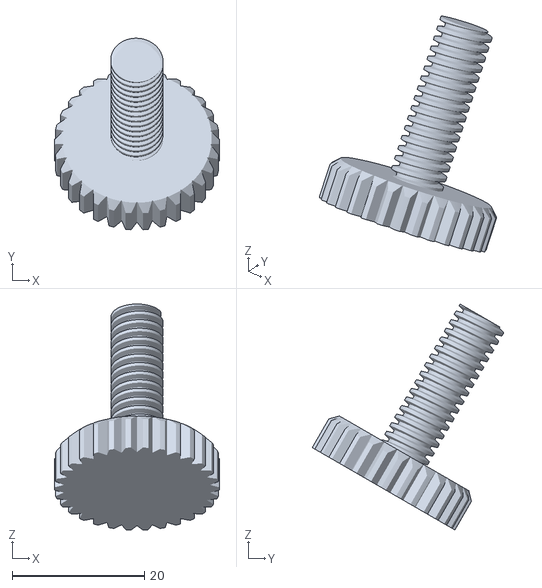
[picture p81: CAD file, 2023-05-18]
STLs/Game Board/Universal Foot Integrated.stl
25.0 x 29.0 x 34.2
