BluGeni/Hextraction/STLs/Game Board/Basic Clip.stl

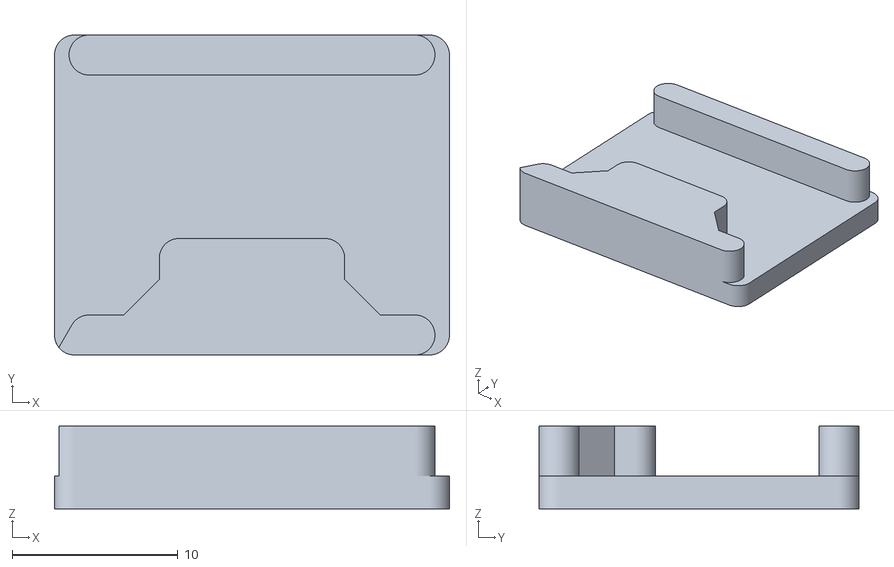
[picture p82: CAD file, 2023-05-18]
STLs/Game Board/Basic Clip.stl
23.9 x 19.3 x 5.00
