BluGeni/Hextraction/STLs/Game Board/Gutter Leg Start.stl

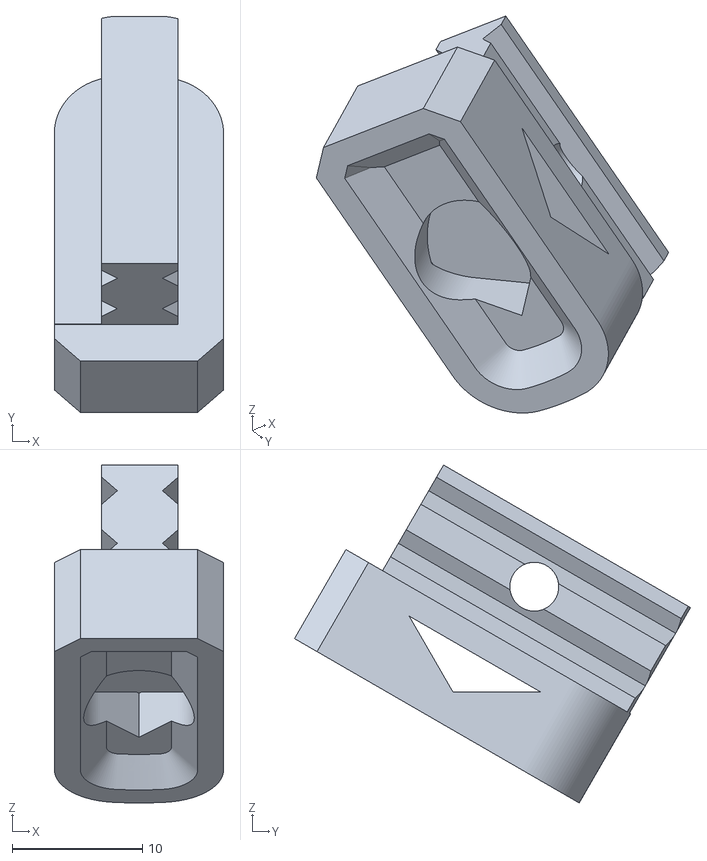
[picture p83: CAD file, 2023-05-18]
STLs/Game Board/Gutter Leg Start.stl
13.0 x 30.4 x 26.0
