BluGeni/Hextraction/STLs/Game Board/Gutter Leg Segment 12mm.stl

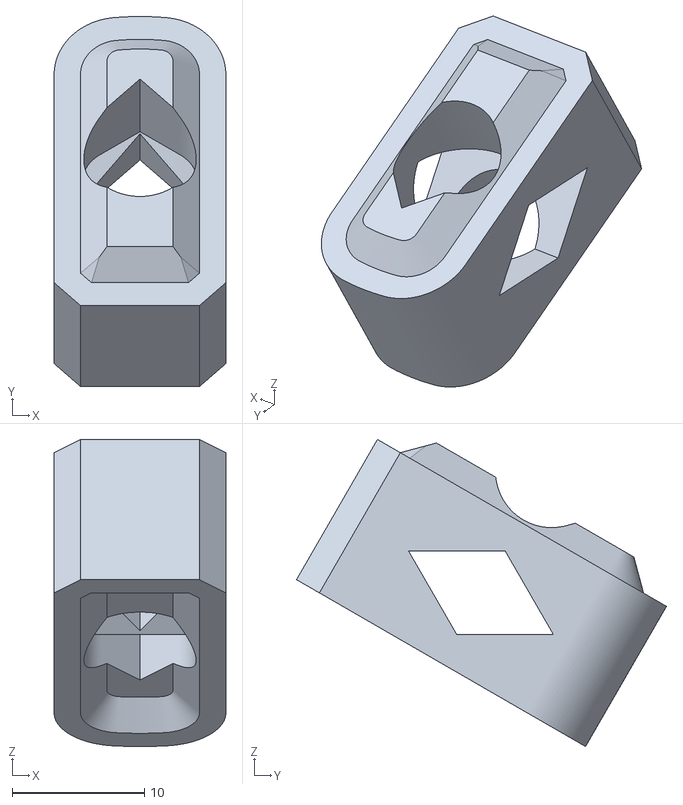
[picture p84: CAD file, 2023-05-18]
STLs/Game Board/Gutter Leg Segment 12mm.stl
13.0 x 28.0 x 23.2
