BluGeni/Hextraction/STLs/Game Board/Basic Front Leg Mount.stl

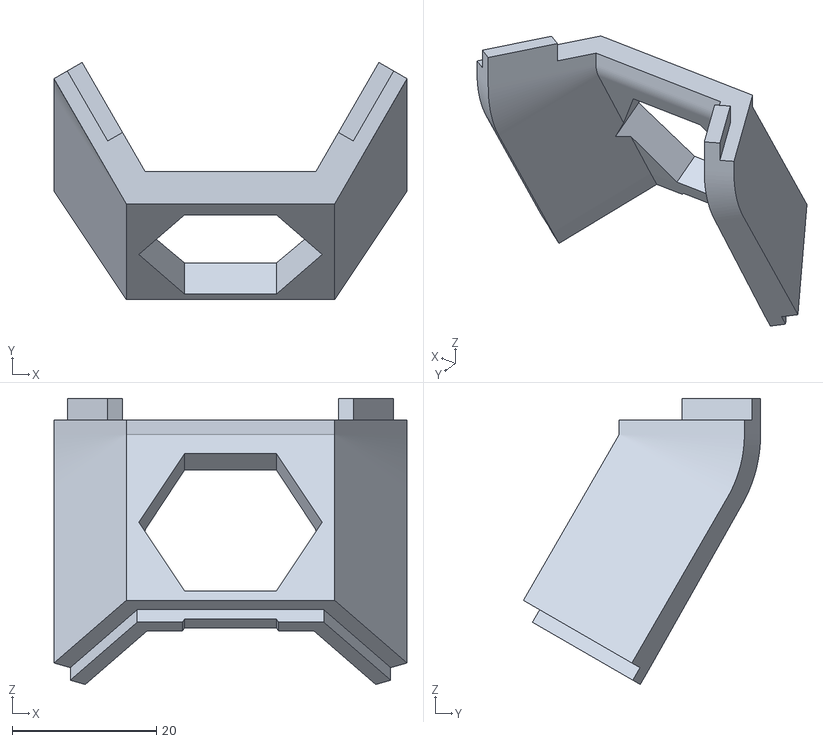
[picture p85: CAD file, 2023-05-18]
STLs/Game Board/Basic Front Leg Mount.stl
48.9 x 32.9 x 39.6
