BluGeni/Hextraction/STLs/Game Board/Basic Leg Segment.stl

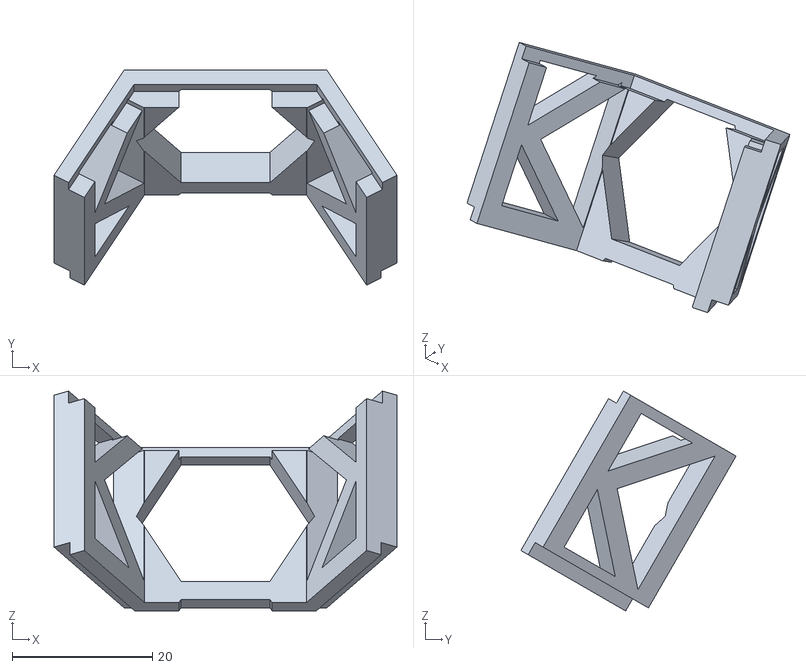
[picture p86: CAD file, 2023-05-18]
STLs/Game Board/Basic Leg Segment.stl
48.9 x 30.7 x 31.4
