BluGeni/Hextraction/STLs/Game Board/Basic Leg Segment 50mm.stl

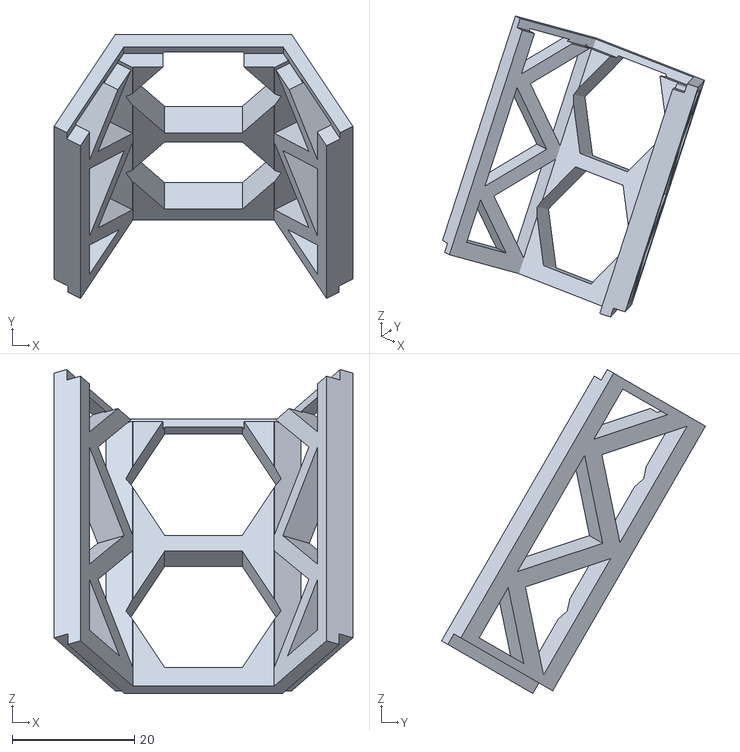
[picture p87: CAD file, 2023-05-18]
STLs/Game Board/Basic Leg Segment 50mm.stl
48.9 x 43.2 x 53.0
