BluGeni/Hextraction/STLs/Game Board/Basic Back Leg Mount.stl

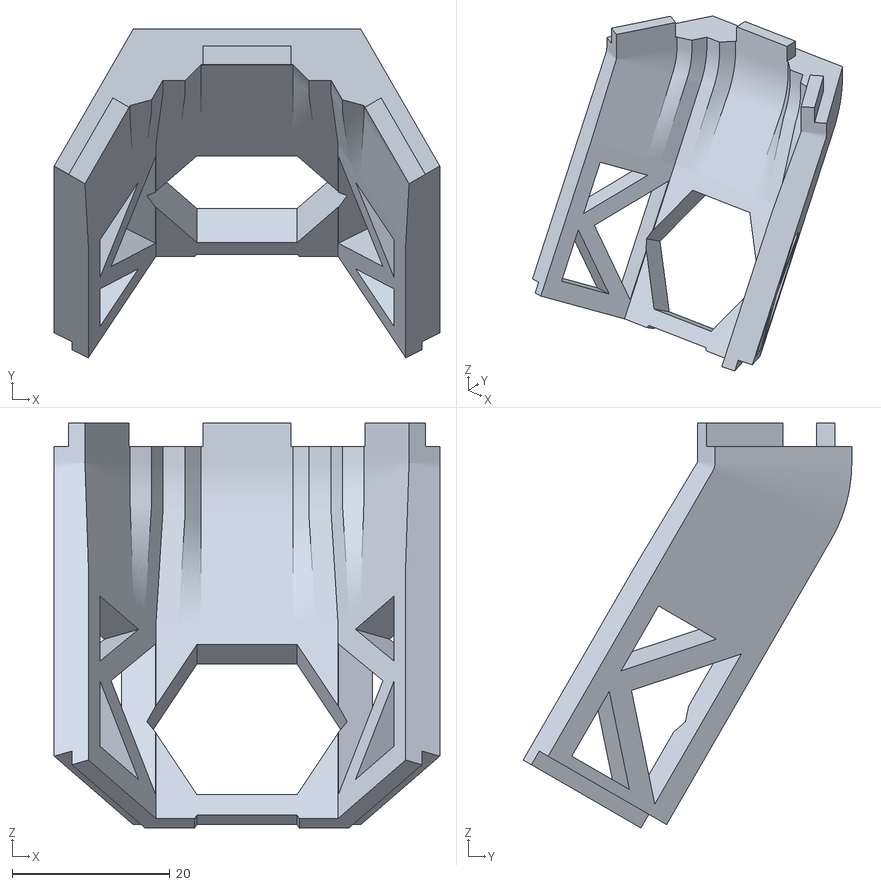
[picture p88: CAD file, 2023-05-18]
STLs/Game Board/Basic Back Leg Mount.stl
48.9 x 41.7 x 51.4
