BluGeni/Hextraction/STLs/Game Board/Gutter Endcap.stl

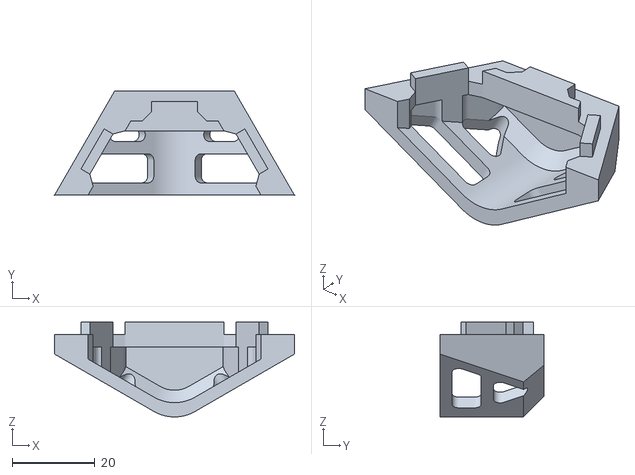
[picture p89: CAD file, 2023-05-18]
STLs/Game Board/Gutter Endcap.stl
58.0 x 25.2 x 22.9
